TobiasVanDyk/VS1053-Micro-Midi-Synthesizer/images/Sparkfun-Adafruit.jpg

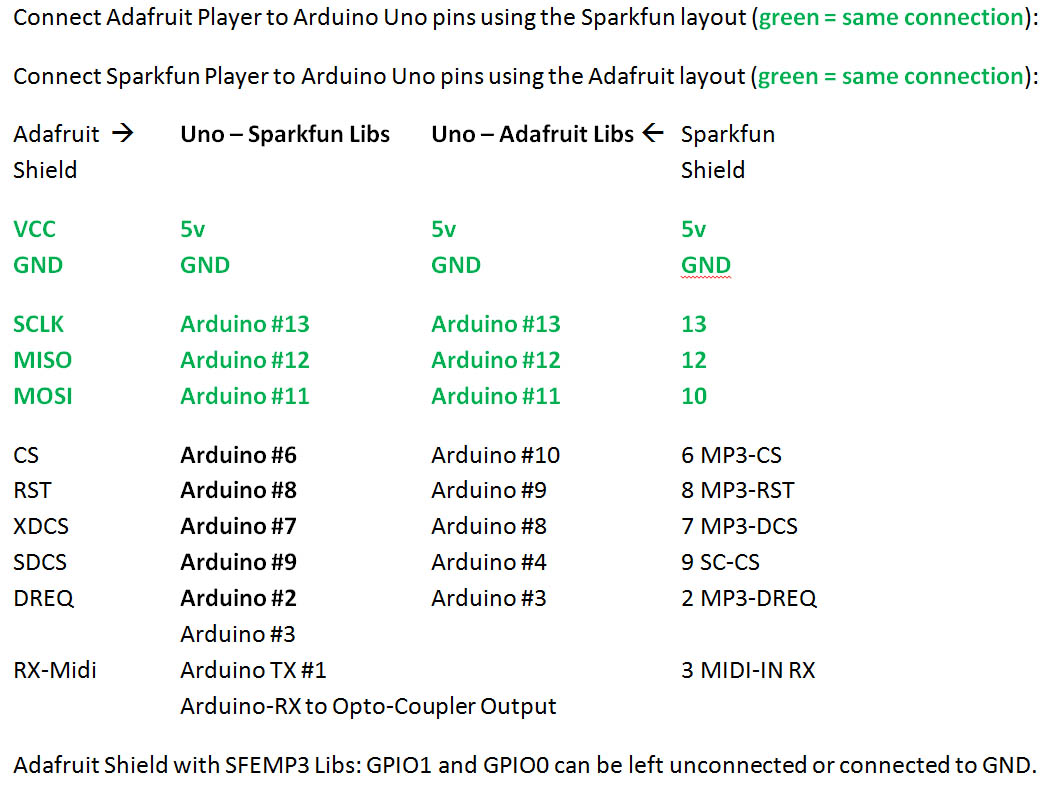
images/Sparkfun-Adafruit.jpg
