TobiasVanDyk/VS1053-Micro-Midi-Synthesizer/images/Sparkfun.jpg

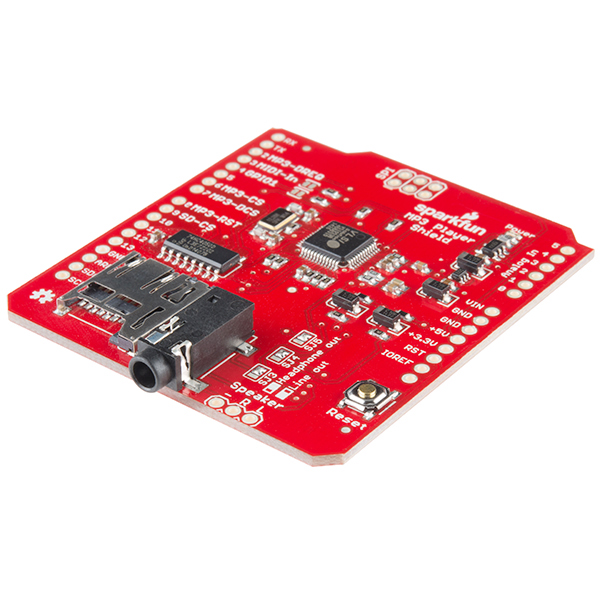
images/Sparkfun.jpg
